zeus074/dramtester/IMG/IMG_6066.jpg

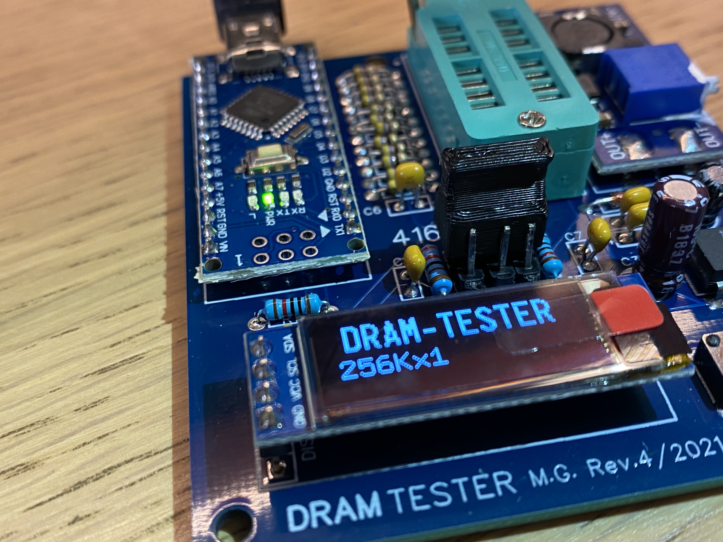
IMG/IMG_6066.jpg
